hanshanaweerakoon/Analog-Voice-Over-Circuit-/simulation/Final.asc

3.5mm_Audio: voltage; SINE(0 1 1000)
C1: cap; 47µ
C2: cap; 0.22µ
C3: cap; 470µ
C4: cap; 100n
C5: cap; 470µ
C6: cap; 470µ
C7: cap; 470µ
D1: diode; 1N4148
D2: diode; 1N4148
D3: diode; 1N4148
D4: diode; 1N4148
D5: diode; 1N4148
Mic: res; 2.2k
Q1: npn; 2N3904
Q2: pnp; D45H11
R1: res; 100k
R2: res; 10k
R3: res; 100k
R4: res; 10k
R5: res; 100k
R6: res; 5k
R7: res; 10k
R8: res; 10k
R9: res; 10k
R10: res; 10k
R11: res; 20k
R12: res; 20k
R13: res; 100k
R14: res; 2k
R15: res; 10k
R16: res; 10k
R17: res; 3.33k
R18: res; 100k
R19: res; 10k
R20: res; 10k
R21: res; 500
Speaker: res; 8
U1: TL072
U2: TL072
U3: TL072
U4: TL072
U5: TL072
U6: CD4066
U7: TL072
U8: CD4066
U9: TL072
V1: voltage; 12
V2: voltage; 12
Variable_Res: res; 100k
Named nets: 0
-
+
TIP41
TIP42
.tran 10m
n1
n2
n3
+
+
+
+
n5
n6
n4
